indifferentengine/ModularPedalboard/Photos/Adam Paul's Prototype Board/Top1.jpg

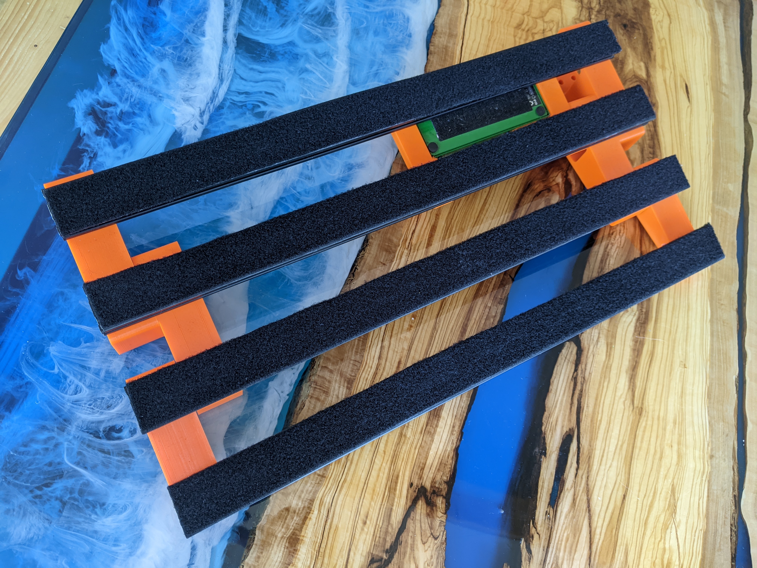
Photos/Adam Paul's Prototype Board/Top1.jpg
