indifferentengine/ModularPedalboard/Renders/Rear1.PNG

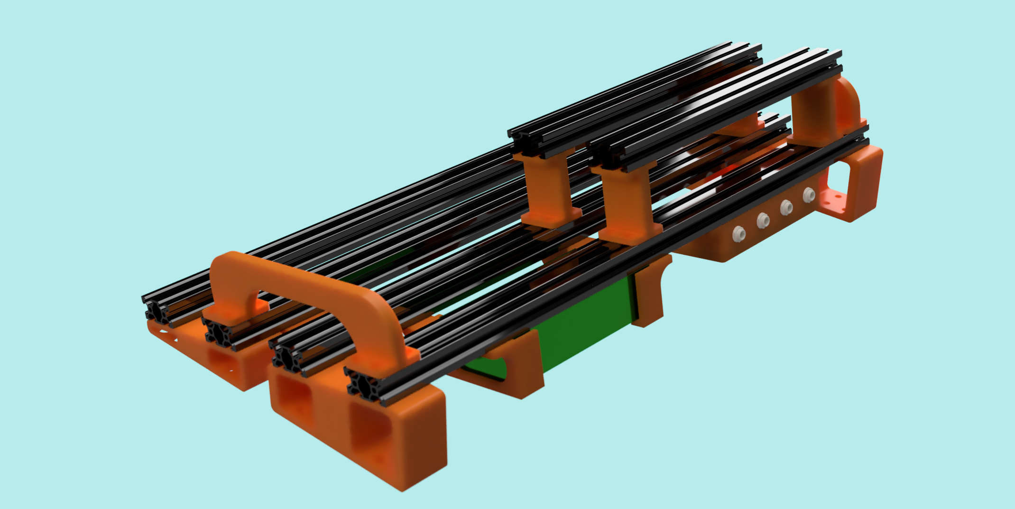
Renders/Rear1.PNG
