indifferentengine/ModularPedalboard/Renders/side1.PNG

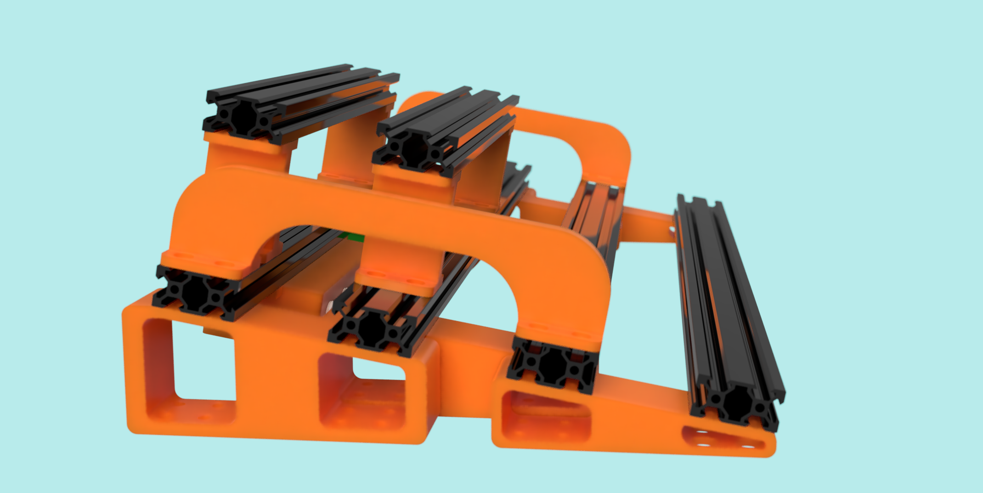
Renders/side1.PNG
