indifferentengine/ModularPedalboard/STL/part-brace-F3toF4.stl

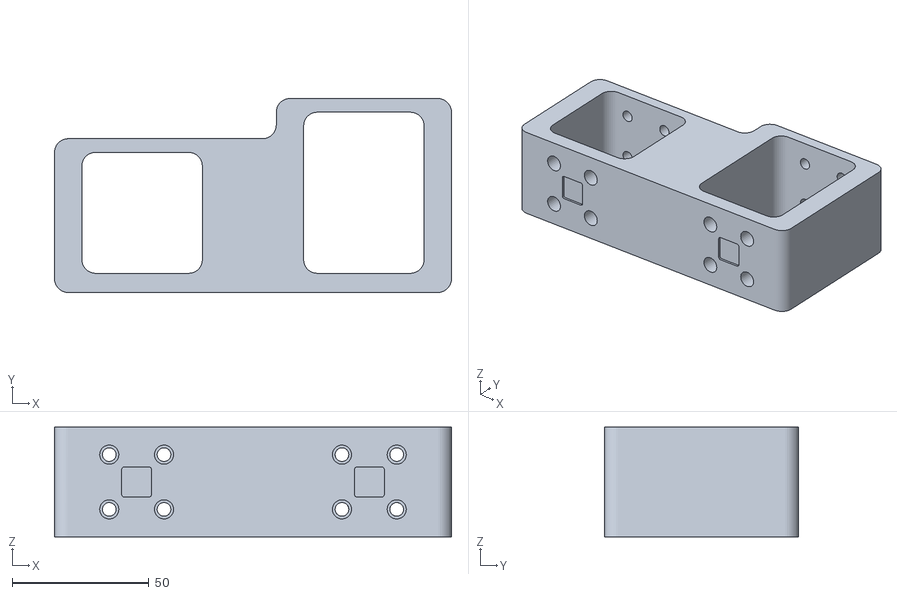
[picture p34: CAD file, 2026-09-29]
STL/part-brace-F3toF4.stl
145.0 x 70.9 x 40.0
