indifferentengine/ModularPedalboard/STL/part-brace-F2.stl

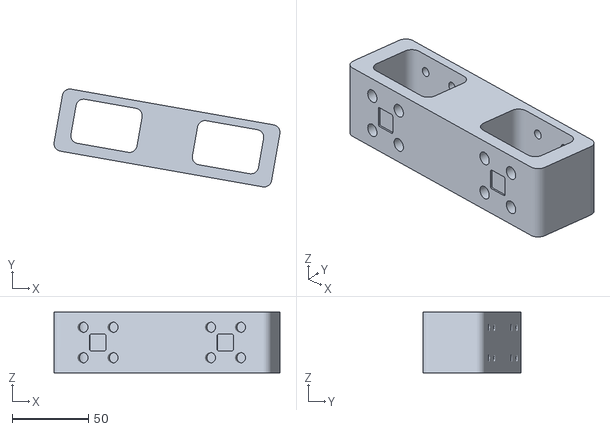
[picture p35: CAD file, 2026-09-29]
STL/part-brace-F2.stl
148.4 x 64.3 x 40.0
