indifferentengine/ModularPedalboard/STL/part-brace-A4toF4.stl

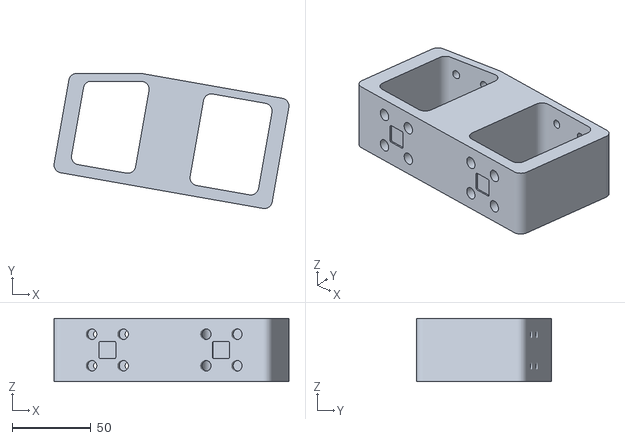
[picture p36: CAD file, 2026-09-29]
STL/part-brace-A4toF4.stl
148.9 x 85.6 x 40.0
