indifferentengine/ModularPedalboard/STL/part-brace-F1toF2.stl

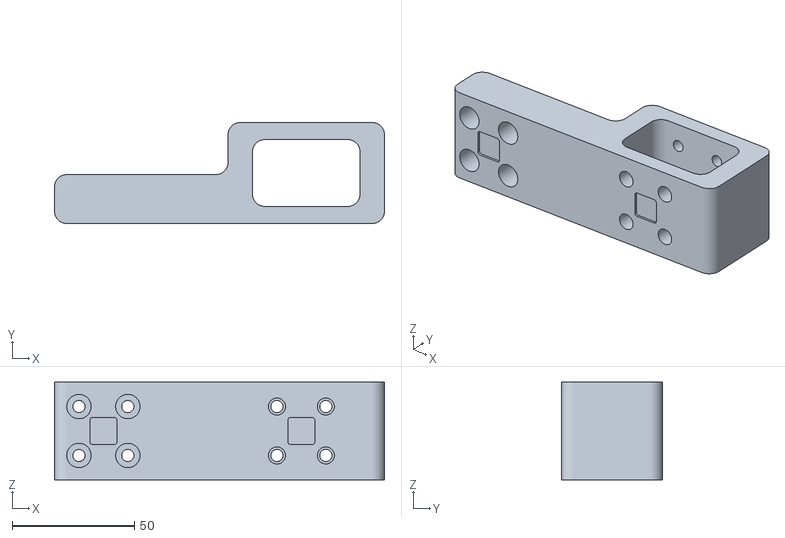
[picture p37: CAD file, 2026-09-29]
STL/part-brace-F1toF2.stl
135.0 x 41.3 x 40.0
