indifferentengine/ModularPedalboard/STL/part-brace-F2toF3.stl

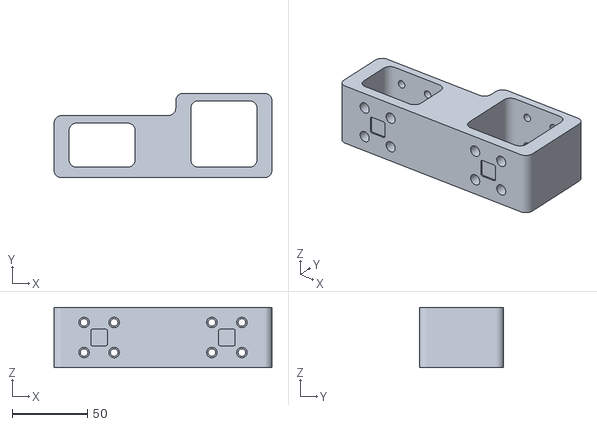
[picture p38: CAD file, 2026-09-29]
STL/part-brace-F2toF3.stl
145.0 x 56.2 x 40.0
