indifferentengine/ModularPedalboard/STL/part-brace-A3toF3.stl

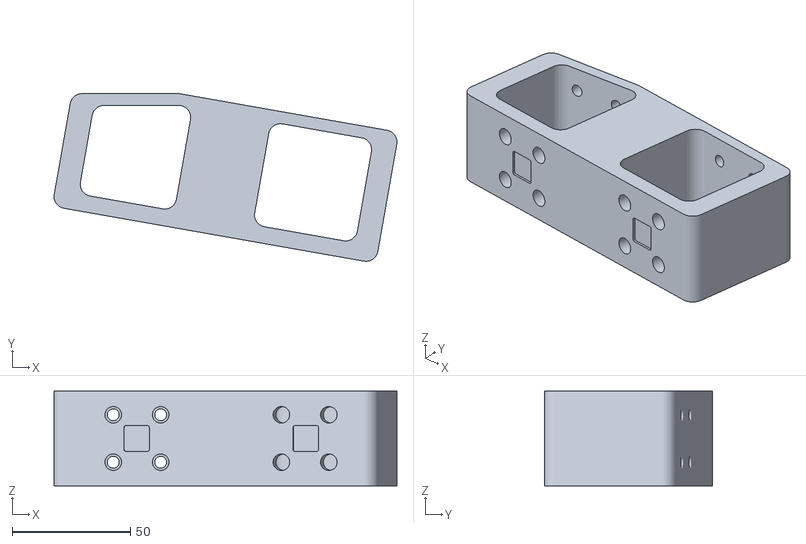
[picture p39: CAD file, 2026-09-29]
STL/part-brace-A3toF3.stl
144.7 x 70.8 x 40.0
