indifferentengine/ModularPedalboard/STL/part-brace-F2toF4.stl

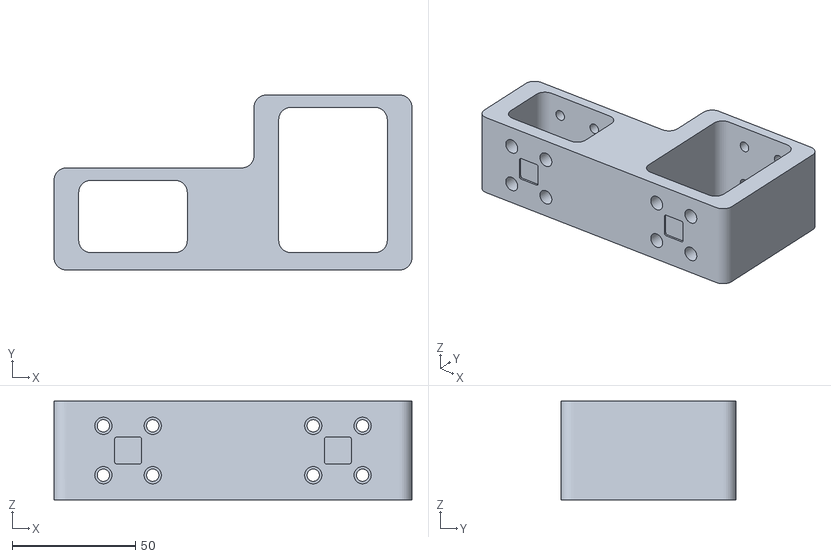
[picture p40: CAD file, 2026-09-29]
STL/part-brace-F2toF4.stl
145.0 x 70.9 x 40.0
