indifferentengine/ModularPedalboard/STL/part-tiersupport1.stl

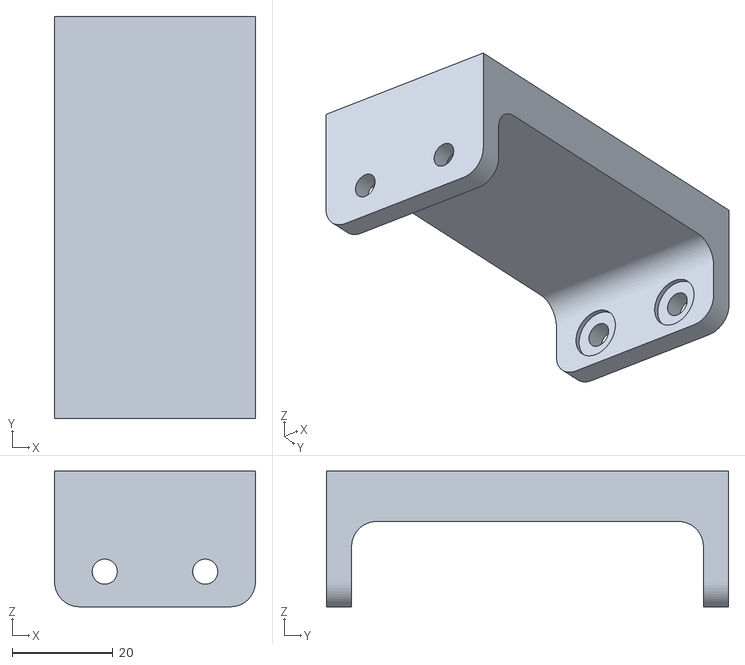
[picture p41: CAD file, 2026-09-29]
STL/part-tiersupport1.stl
40.0 x 80.0 x 27.0
