indifferentengine/ModularPedalboard/STL/part-brace-F1toA1.stl

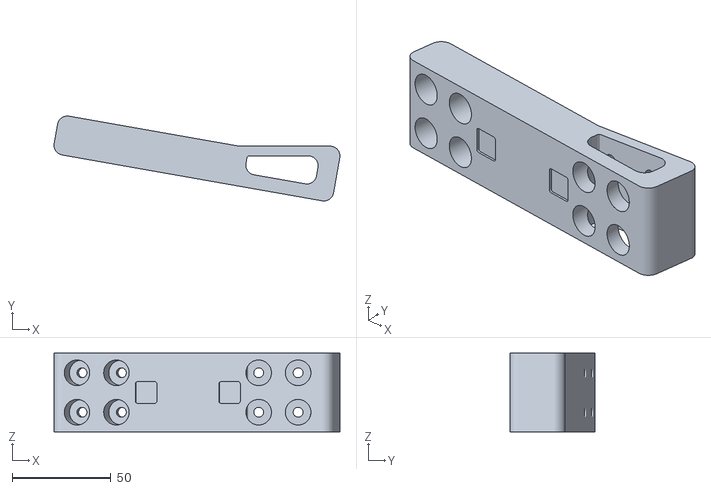
[picture p42: CAD file, 2026-09-29]
STL/part-brace-F1toA1.stl
145.1 x 43.1 x 40.0
