indifferentengine/ModularPedalboard/STL/part-brace-A5toF5.stl

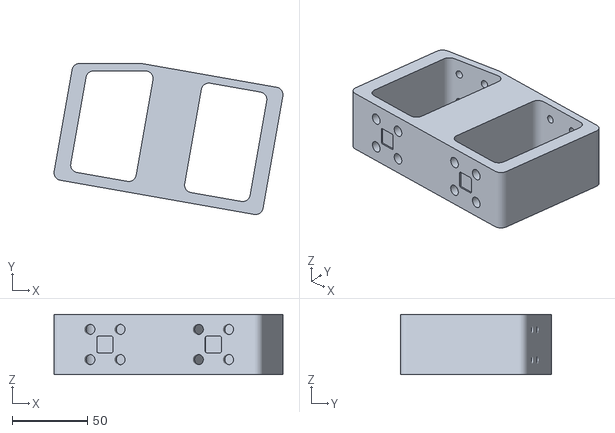
[picture p43: CAD file, 2026-09-29]
STL/part-brace-A5toF5.stl
151.8 x 100.2 x 40.0
