indifferentengine/ModularPedalboard/STL/part-brace-A4.stl

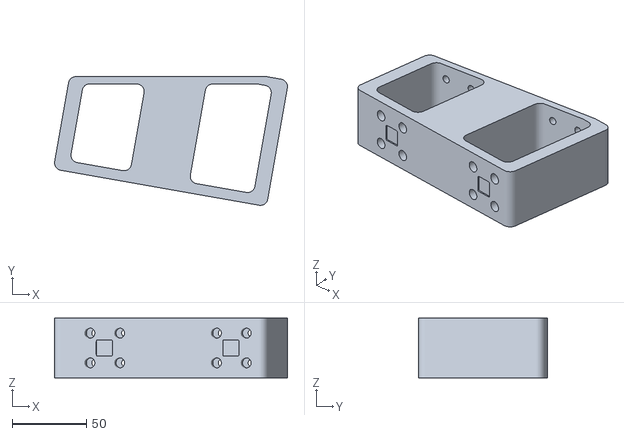
[picture p44: CAD file, 2026-09-29]
STL/part-brace-A4.stl
156.6 x 86.5 x 40.0
